adct-the-experimenter/ms-circuit-video-game/test-circuits/ltspice-circuits/zero-crossing-detector-derivative.asc

C1: cap; 0.1µ
C2: cap; 100p
D1: diode; 1N914
D2: diode; 1N914
D3: diode; 1N914
D4: diode; 1N914
R1: res; 10k
R2: res; 10k
R3: res; 10k
R4: res; 10k
R5: res; 5k
R6: res; 10k
R7: res; 10k
R8: res; 10k
R9: res; 10k
U1: UniversalOpamp2
U2: UniversalOpamp2
U3: UniversalOpamp2
U4: UniversalOpamp2
V1: voltage; 3
V2: voltage; -3
V4: voltage; SINE(1.0 2.0 50); AC 1
Named nets: 0, VCC, VEE, dir_detect, Vin, zero_detect, abs_zero_cross
;tran 0 0.5s 0 10us
.ac dec 10 1 1G
differentiatior to take derivative of direction detection to detect zero cross.
