adct-the-experimenter/ms-circuit-video-game/test-circuits/ltspice-circuits/sample-and-hold.asc

C1: cap; 100n
M1: nmos; RUL035N02
U1: UniversalOpamp2
U2: UniversalOpamp2
V1: voltage; -3
V2: voltage; 3
V3: voltage; SINE(2.5 2.5 1k); AC 1
V5: voltage; SINE(1 2 0.1k); AC 1
Named nets: VCC, VEE, 0, input_signal, sample, output, in_buffer
Sample/hold control
.tran 0 0.1s 0 10us
;ac dec 10 1 1G
.op
Sample at 5V, hold at 0V
Note: Mosfet resistance and capacitor can form a filter with RC time constant.
nmos should be operated in triode region to act as a switch with little on resistance.
