adct-the-experimenter/ms-circuit-video-game/test-circuits/ltspice-circuits/collision-detector-1d.asc

C1: cap; 500p
C2: cap; 50n
D1: diode; 1N914
D2: diode; 1N914
D3: diode; 1N914
D4: diode; 1N914
R1: res; 10k
R2: res; 10k
R3: res; 10k
R4: res; 10k
R5: res; 10k
R6: res; 10k
R7: res; 10k
R8: res; 10k
R9: res; 5k
R10: res; 10k
R11: res; 10k
R12: res; 10k
R13: res; 10k
U1: UniversalOpamp2
U2: UniversalOpamp2
U3: UniversalOpamp2
U4: UniversalOpamp2
U5: UniversalOpamp2
V1: voltage; 3
V2: voltage; -3
V3: voltage; SINE(1 2 10 0 0 90)
V4: voltage; SINE(2.5 2.5 50)
V5: voltage; 2
V6: voltage; 2
V7: voltage; PULSE(0 5.0 0 0.05 0.05 0.1)
Named nets: VCC, VEE, 0, vout_diff, Player_X, Opponent_Weapon_X, abs_zero_cross, zero_detect, dir_detect
.tran 0 0.5s 0 10us
;ac dec 10 1 1G
