adct-the-experimenter/ms-circuit-video-game/test-circuits/ltspice-circuits/collision-detector-2d-add-sub.asc

C1: cap; 0.1µ
C2: cap; 50n
D1: diode; 1N914
D2: diode; 1N914
D3: diode; 1N914
D4: diode; 1N914
R1: res; 10k
R2: res; 5k
R3: res; 10k
R4: res; 10k
R5: res; 10k
R6: res; 10k
R7: res; 10k
R8: res; 10k
R9: res; 10k
R10: res; 10k
R11: res; 10k
R12: res; 10k
R13: res; 10k
R14: res; 10k
R15: res; 10k
R16: res; 10k
R17: res; 10k
R18: res; 10k
R19: res; 5k
R20: res; 10k
R21: res; 10k
R25: res; 10k
R26: res; 10k
R27: res; 10k
R28: res; 10k
R29: res; 10k
R30: res; 10k
R31: res; 10k
R32: res; 5k
U1: UniversalOpamp2
U2: UniversalOpamp2
U3: UniversalOpamp2
U4: UniversalOpamp2
U5: UniversalOpamp2
U6: UniversalOpamp2
U7: UniversalOpamp2
U8: UniversalOpamp2
U9: UniversalOpamp2
V1: voltage; 3
V2: voltage; -3
V3: voltage; SINE(1 2 1k); AC 1
V4: voltage; 1; AC 1
V5: voltage; 1; AC 1
V6: voltage; 1; AC 1
Named nets: 0, VCC, VEE, W1x, P2x, W1y, P2y, xdiff, ydiff, xdiff+ydiff, xdiff-ydiff, diffsum_result, dir_detect, zero_detect, collision_detect
.tran 0 0.1s 0 10us
;ac dec 10 1 1G
Collision Detection
Weapon Player 1 against Player 2
makes collision detection go high to supply voltage.
No difference between x and y coordinates of player 1 weapon and player 2 position
Weapon Player 1
Player 2
xdiff - ydiff
xdiff
ydiff
(xdiff - ydiff) + (xdiff + ydiff)
xdiff + ydiff
Special Note: order doesn't matter for subtraction in the case that both numbers are zero
Postive only zero cross detector circuit
