adct-the-experimenter/ms-circuit-video-game/test-circuits/ltspice-circuits/summer.asc

C1: cap; 1µ
C3: cap; 1p
R1: res; 10k
R2: res; 10k
R3: res; 10k
R4: res; 10k
R5: res; 5k
R6: res; 1k
R7: res; 100k
R8: res; 5k
R9: res; 10k
R16: res; 50k
R17: res; 50k
R18: res; 50k
R19: res; 50k
U1: UniversalOpamp2
U2: UniversalOpamp2
U3: UniversalOpamp2
V1: voltage; 3
V2: voltage; -3
V3: voltage; SINE(2.5 2.5 100)
Named nets: VCC, VEE, 0, Pposx, Wposx, Vout_wcox
.tran 0 0.5s 0 10us startup uic
