adct-the-experimenter/ms-circuit-video-game/console-hardware/system-hardware/ltspice-test-circuits/neg-voltage-rail.asc

C1: polcap; 100n
C2: polcap; 10µ
C3: polcap; 4.7µ
C4: polcap; 2.2µ
D1: schottky; MBR0520L
L1: ind; 4.7µ
R1: res; 14.7k
R2: res; 2.8k
RLoad: res; 10k
U1: ADP2300
V1: voltage; 5
Named nets: 0, vout_neg_reg, VCC
;op
Circuit adapted from application note AN-1083.pdf Figure 8 reference design 4
.tran 0 0.5 0 0.1 steady
