adct-the-experimenter/ms-circuit-video-game/games/switched-tag/analog-module/simulation/attack-mechanic.asc

C3: cap; 3.3µ
C4: cap; 1µ
C5: cap; 3.3µ
C6: cap; 1µ
D1: diode; 1N914
D2: diode; 1N914
R1: res; 10k
R2: res; 10k
R3: res; 10k
R4: res; 10k
R5: res; 10k
R6: res; 10k
R7: res; 10k
R12: res; 10k
R13: res; 10k
R15: res; 10k
R16: res; 10k
U2: UniversalOpamp2
U4: UniversalOpamp2
U5: UniversalOpamp2
U6: UniversalOpamp2
V1: voltage; -3
V2: voltage; 3
V3: voltage; PULSE(0 3.3 0.1 0.002 0.002 0.5); AC 1
V4: voltage; PULSE(0 3.3 0.15 0.002 0.002 1); AC 1
Named nets: 0, VCC, VEE, diff, P2_it, P1_it, P1_it_val, P1_button_input, P2_button_input, P2_it_val
Circuit to determine which player is It.
.tran 0 2s 0 0.1s
;ac dec 10 1 1G
.op
P2_val - P1_val
Find difference between player values
Take rate of change of button press. Positive wave form on release
Push-button switch is modelled as a square wave with 2 ms rise time and fall time.
i.e. has the highest attack value.
Differentiator stats
F_low = 1 / (Cin*Rfeedback) = 30 Hz
F_high = 1 / (Cfeedback*Rin) = 100 Hz
DC Gain = Rfeedback / Rin = 1 = 0 dB
