adct-the-experimenter/ms-circuit-video-game/games/switched-tag/analog-module/simulation/collision-detection-simple.asc

D1: diode; 1N914
D2: diode; 1N914
D3: diode; 1N914
D4: diode; 1N914
D5: diode; 1N914
R1: res; 10k
R2: res; 10k
R3: res; 10k
R4: res; 10k
R5: res; 10k
R6: res; 10k
R7: res; 10k
R8: res; 10k
R9: res; 10k
R10: res; 10k
R11: res; 10k
R12: res; 5k
R13: res; 10k
R14: res; 10k
R15: res; 5k
R16: res; 10k
R17: res; 10k
R18: res; 10k
R19: res; 5k
R20: res; 10k
R21: res; 10k
R22: res; 10k
R23: res; 100k
R24: res; 5k
R25: res; 10k
U1: UniversalOpamp2
U2: UniversalOpamp2
U3: UniversalOpamp2
U4: UniversalOpamp2
U5: UniversalOpamp2
U6: UniversalOpamp2
U7: UniversalOpamp2
U8: UniversalOpamp2
V1: voltage; -3.3
V2: voltage; 3.3
V3: voltage; SINE(1.5 1.5 10); AC 1
V4: voltage; 1; AC 1
V5: voltage; 0.5; AC 1
V6: voltage; SINE(1 0.5 10); AC 1
Named nets: VCC, VEE, 0, P1x, P2x, P1y, P2y, xdiff, ydiff, abs_xdiff, abs_ydiff, abs_sum_xdiff_ydiff, collision_detect
Player 1 vs Player 2
makes collision detection go high to supply voltage.
No difference between x and y coordinates of player 1 and player 2 position
xdiff
ydiff
abs(xdiff) + abs(ydiff)
Player 1
Player 2
.tran 2
abs(xdiff)
abs(ydiff)
Comparator
