adct-the-experimenter/ms-circuit-video-game/games/switched-tag/analog-module/simulation/switched-tag-v2.asc

C1: cap; 3.3µ
C2: cap; 1µ
C3: cap; 3.3µ
C4: cap; 1µ
D1: diode; 1N914
D2: diode; 1N914
D3: diode; 1N914
D4: diode; 1N914
D9: diode; 1N914
D10: diode; 1N914
D11: diode; 1N914
M3: nmos; RUL035N02
M4: nmos; RUL035N02
M5: nmos; RUL035N02
R1: res; 10k
R2: res; 10k
R3: res; 10k
R4: res; 10k
R5: res; 10k
R6: res; 10k
R7: res; 10k
R8: res; 10k
R9: res; 10k
R10: res; 10k
R11: res; 5k
R12: res; 10k
R13: res; 10k
R14: res; 10k
R15: res; 100k
R16: res; 5k
R17: res; 10k
R18: res; 10k
R19: res; 10k
R20: res; 5k
R21: res; 10k
R22: res; 10k
R23: res; 10k
R24: res; 10k
R25: res; 10k
R26: res; 10k
R27: res; 5k
R28: res; 10k
R29: res; 10k
R30: res; 10k
R31: res; 10k
R32: res; 10k
R33: res; 10k
R34: res; 10k
R35: res; 10k
R36: res; 10k
R37: res; 10k
R38: res; 10k
R43: res; 10k
R44: res; 10k
R45: res; 10k
U1: UniversalOpamp2
U2: UniversalOpamp2
U3: UniversalOpamp2
U4: UniversalOpamp2
U5: UniversalOpamp2
U6: UniversalOpamp2
U7: UniversalOpamp2
U8: UniversalOpamp2
U9: UniversalOpamp2
U10: UniversalOpamp2
U11: UniversalOpamp2
U20: UniversalOpamp2
V1: voltage; -3.3
V2: voltage; 3.3
V3: voltage; 1; AC 1
V4: voltage; SINE(1.5 1.5 10); AC 1
V5: voltage; 1; AC 1
V6: voltage; 1; AC 1
V7: voltage; PULSE(0 3 0.5 0.1 0.1 2); AC 1
V8: voltage; PULSE(0 3 1 0.1 0.1 1); AC 1
V9: voltage; SINE(1.5 1.5 10); AC 1
V10: voltage; 1; AC 1
V13: voltage; PULSE(0 3.3 0.1 0.002 0.002 0.5); AC 1
V14: voltage; PULSE(0 3.3 0.1 0.002 0.002 1); AC 1
Named nets: 0, VCC, VEE, P1y, P2y, P2x, P1x, P1_button_it, P2_button_it, xdiff, ydiff, abs_xdiff, abs_ydiff, abs_sum_xdiff_ydiff, collision_detect, P1_it, P2_it, p2_win, p1_win, two_winner_ignore, pendelum, P2_it_val, P1_it_val, P1_switch_weapon, P2_switch_weapon, diff, P1_button_input, P2_button_input
Switch Tag
Input
Logic
Output
It player determination
Collision Detection
Player 1 vs Player 2
makes collision detection go high to supply voltage.
No difference between x and y coordinates of player 1 and player 2 position
.tran 0 2s 0 0.1s
;ac dec 10 1 1G
Player 1
Player 2
Sample at 5V, hold at 0V
xdiff
ydiff
abs(xdiff + ydiff)
Postive only zero cross detector circuit
Winner Determination
op-amp modeled is LM358A.
Take a sample of each value for drawing to display. 60 frames per second drawn.
ADC has sample and hold circuit. The sampling rate of ADC should be 2x highest frequency of analog output.
Due to multi-channel op-amp using diode instead of gnd in op-amp.
Circuit to determine which player is It.
P2_val - P1_val
Find difference between player values
Take rate of change of button press. Positive wave form on release
Push-button switch is modelled as a square wave with 2 ms rise time and fall time.
i.e. has the highest attack value.
