adct-the-experimenter/ms-circuit-video-game/games/switched-tag/analog-module/simulation/pendelum-model.asc

C1: cap; 2.2µ
R1: res; 100k
R2: res; 10k
R3: res; 10k
U1: UniversalOpamp2
U2: UniversalOpamp2
U3: UniversalOpamp2
V1: voltage; 3
V2: voltage; -3
Named nets: 0, VCC, VEE, pendelum
.tran 0 1s 0 10us startup uic
Using triangle wave instead of square wave since need more than 2 values for comparison.
frequency: ( 1 / (4*R1*C1) ) * ( R3 / R2 )
triangle wave volt output: VCC*( R2 / R3 )
Has low impedance input.
