adct-the-experimenter/ms-circuit-video-game/games/switched-tag/analog-module/simulation/it-player-determination.asc

C1: cap; 100n
C2: cap; 100n
D3: diode; 1N914
D4: diode; 1N914
M1: nmos; RUL035N02
M2: nmos; RUL035N02
R1: res; 10k
R2: res; 10k
R3: res; 10k
R4: res; 10k
R7: res; 10k
R8: res; 10k
R9: res; 10k
R10: res; 10k
R11: res; 5k
R12: res; 10k
R13: res; 5k
U1: UniversalOpamp2
U2: UniversalOpamp2
U3: UniversalOpamp2
U4: UniversalOpamp2
U5: UniversalOpamp2
U7: UniversalOpamp2
U8: ADG419
U9: ADG419
V1: voltage; -3
V2: voltage; 3
V3: voltage; SINE(2.5 2.5 100); AC 1
V4: voltage; PULSE(0 3 0.5 0.1 0.1 1); AC 1
V5: voltage; PULSE(0 3 1 0.1 0.1 1); AC 1
V6: voltage; 3
V7: voltage; 3
Named nets: 0, VCC, VEE, pendelum, P1_button_it, pend_buffer1, pend_buffer2, P2_button_it, diff, P1_it_val, P2_it_val, P2_it, P1_it, P1_switch_weapon, P2_switch_weapon
Circuit to determine which player is It.
.tran 0 2s 0 0.1s
;ac dec 10 1 1G
.op
Sample at 5V, hold at 0V
Sample/hold control
Sample/hold control
Sample Input from Players
Compare difference from low-point of pendelum (5 V)
difference between player 1 and player 2.
Order matters in subtraction here. Negative means player 1 has higher value, positive means player 2 has higher value.
Whichever player has highest  value in magnitude is closest to low-point of pendelum and is it.
Output
It player( 0V player is not it, 4.5V player is it)
Modelling button press.
Winner Determination
