adct-the-experimenter/ms-circuit-video-game/games/switched-tag/analog-module/ltspice-circuit/switched-tag.asc

C1: cap; 0.1µ
C2: cap; 100p
C3: cap; 2µ
C4: cap; 0.1µ
C5: cap; 0.1µ
D1: diode; 1N914
D2: diode; 1N914
D3: diode; 1N914
D4: diode; 1N914
D5: diode; 1N914
D6: diode; 1N914
D7: diode; 1N914
D8: diode; 1N914
M1: nmos; RUL035N02
M2: nmos; RUL035N02
M3: nmos; RUL035N02
M4: nmos; RUL035N02
M5: nmos; RUL035N02
R1: res; 10k
R2: res; 10k
R3: res; 10k
R4: res; 10k
R5: res; 10k
R6: res; 10k
R7: res; 10k
R8: res; 10k
R9: res; 10k
R10: res; 10k
R11: res; 10k
R12: res; 5k
R13: res; 10k
R14: res; 10k
R15: res; 10k
R16: res; 10k
R17: res; 10k
R18: res; 10k
R19: res; 10k
R20: res; 5k
R21: res; 10k
R22: res; 10k
R23: res; 10k
R24: res; 10k
R25: res; 10k
R26: res; 10k
R27: res; 5k
R28: res; 10k
R29: res; 10k
R30: res; 100k
R31: res; 10k
R32: res; 10k
R33: res; 10k
R34: res; 10k
R35: res; 10k
R36: res; 10k
R37: res; 10k
R38: res; 10k
R39: res; 10k
R41: res; 10k
R42: res; 10k
R43: res; 1k
R44: res; 1k
R45: res; 1k
U1: UniversalOpamp2
U2: UniversalOpamp2
U3: UniversalOpamp2
U4: UniversalOpamp2
U5: UniversalOpamp2
U6: UniversalOpamp2
U7: UniversalOpamp2
U8: UniversalOpamp2
U9: UniversalOpamp2
U10: UniversalOpamp2
U11: UniversalOpamp2
U12: UniversalOpamp2
U13: UniversalOpamp2
U14: UniversalOpamp2
U15: UniversalOpamp2
U16: UniversalOpamp2
U17: UniversalOpamp2
U18: UniversalOpamp2
U19: UniversalOpamp2
V1: voltage; -3.3
V2: voltage; 3.3
V3: voltage; SINE(1.5 1.5 10); AC 1
V4: voltage; 1; AC 1
V5: voltage; 1; AC 1
V6: voltage; 1; AC 1
V7: voltage; PULSE(0 3 0.5 0.1 0.1 2); AC 1
V8: voltage; PULSE(0 3 1 0.1 0.1 1); AC 1
Named nets: 0, VCC, VEE, P1y, P2y, P2x, P1x, P1_it_val, pend_buffer1, P1_button_it, pendelum, P2_it_val, pend_buffer2, P2_button_it, it_value_diff, dir_detect_it, P2_it, P1_it, xdiff, ydiff, xdiff+ydiff, xdiff-ydiff, diffsum_result, dir_detect_collision, zero_detect_collision, collision_detect, p2_win, p1_win, two_winner_ignore
Switch Tag
Input
Logic
Output
It player determination
Collision Detection
Player 1 vs Player 2
makes collision detection go high to supply voltage.
No difference between x and y coordinates of player 1 and player 2 position
.tran 0 2s 0 0.1s
;ac dec 10 1 1G
Player 1
Player 2
Pendelum Model
Sample/hold control
Sample/hold control
Sample at 5V, hold at 0V
xdiff - ydiff
xdiff
ydiff
(xdiff - ydiff) + (xdiff + ydiff)
xdiff + ydiff
Special Note: order doesn't matter for subtraction in the case that both numbers are zero
Postive only zero cross detector circuit
Winner Determination
op-amp modeled is LM358A.
Take a sample of each value for drawing to display. 60 frames per second drawn.
ADC has sample and hold circuit. The sampling rate of ADC should be 2x highest frequency of analog output.
