adct-the-experimenter/ms-circuit-video-game/games/switched-tag/analog-module/simulation/win-determination.asc

M1: nmos; RUL035N02
M2: nmos; RUL035N02
M3: nmos; RUL035N02
R1: res; 1k
R2: res; 1k
R3: res; 1k
V1: voltage; -3
V2: voltage; 3
V3: voltage; PULSE(0 3 0.5 0.1 0.1 1); AC 1
V4: voltage; PULSE(0 3 1 0.1 0.1 1); AC 1
V5: voltage; PULSE(0 3 0.5 0.1 0.1 0.8); AC 1
Named nets: 0, VCC, VEE, P1_it, P2_it, collision_detect, p2_win, p1_win, two_winner_ignore
.op
.tran 0 2s 0 10us
